s13n/AES42HAT/fw/model/I3C0.yaml

# Created from LPC865.svd

name: I3C0
description: I3C
groupName: I3C
registers:
  - name: MCONFIG
    description: Master Configuration Register
    addressOffset: 0
    size: 32
    access: read-write
    resetValue: 0
    resetMask: 4294967291
    fields:
      - name: MSTENA
        description: Master enable
        bitOffset: 0
        bitWidth: 2
        access: read-write
        enumeratedValues:
          - name: MASTER_OFF
            description: 'MASTER_OFF: Master is off (is not enabled). If MASTER_OFF
              is enabled, then the I3C module can only use slave mode.'
            value: 0
          - name: MASTER_ON
            description: 'MASTER_ON: Master is on (is enabled). When used from start-up,
              this I3C module is master by default (the main master). The module will
              control the bus unless the master is handed off. If the master is handed
              off, then MSTENA must move to 2 after that happens. The handoff means
              emitting GETACCMST and if accepted, the module will emit a STOP and
              set the MSTENA bit to 2 (or 0).'
            value: 1
          - name: MASTER_CAPABLE
            description: 'MASTER_CAPABLE: The I3C module is master-capable; however
              the module is operating as a slave now. When used from the start, the
              I3C module will start as a slave, but will be prepared to switch to
              master mode. To switch to master mode, the slave emits an Master Request
              (MR), or gets a GETACCMST CCC command and accepts it (to switch on the
              STOP).'
            value: 2
      - name: DISTO
        description: Disable Timeout
        bitOffset: 3
        bitWidth: 1
        access: read-write
      - name: HKEEP
        description: High-Keeper
        bitOffset: 4
        bitWidth: 2
        access: read-write
        enumeratedValues:
          - name: NONE
            description: 'NONE: Use PUR (Pull-Up Resistor). Hold SCL High.'
            value: 0
          - name: WIRED_IN
            description: 'WIRED_IN: Wired-in High Keeper controls; use pin_HK (High
              Keeper) controls.'
            value: 1
          - name: PASSIVE_SDA
            description: 'PASSIVE_SDA: Passive on SDA; can Hi-Z (high impedance) for
              Bus Free (IDLE) and hold.'
            value: 2
          - name: PASSIVE_ON_SDA_SCL
            description: 'PASSIVE_ON_SDA_SCL: Passive on SDA and SCL; can Hi-Z (high
              impedance) both for Bus Free (IDLE), and can Hi-Z SDA for hold.'
            value: 3
      - name: ODSTOP
        description: Open drain stop
        bitOffset: 6
        bitWidth: 1
        access: read-write
      - name: PPBAUD
        description: Push-pull baud rate
        bitOffset: 8
        bitWidth: 4
        access: read-write
      - name: PPLOW
        description: Push-Pull low
        bitOffset: 12
        bitWidth: 4
        access: read-write
      - name: ODBAUD
        description: Open drain baud rate
        bitOffset: 16
        bitWidth: 8
        access: read-write
      - name: ODHPP
        description: Open drain high push-pull
        bitOffset: 24
        bitWidth: 1
        access: read-write
      - name: SKEW
        description: Skew
        bitOffset: 25
        bitWidth: 3
        access: read-write
      - name: I2CBAUD
        description: I2C baud rate
        bitOffset: 28
        bitWidth: 4
        access: read-write
  - name: SCONFIG
    description: Slave Configuration Register
    addressOffset: 4
    size: 32
    access: read-write
    resetValue: 0
    resetMask: 4278125439
    fields:
      - name: SLVENA
        description: Slave enable
        bitOffset: 0
        bitWidth: 1
        access: read-write
      - name: NACK
        description: Not acknowledge
        bitOffset: 1
        bitWidth: 1
        access: read-write
      - name: MATCHSS
        description: Match START or STOP
        bitOffset: 2
        bitWidth: 1
        access: read-write
      - name: S0IGNORE
        description: S0/S1 errors ignore
        bitOffset: 3
        bitWidth: 1
        access: read-write
      - name: DDROK
        description: Double Data Rate OK
        bitOffset: 4
        bitWidth: 1
        access: read-write
      - name: IDRAND
        description: ID random
        bitOffset: 8
        bitWidth: 1
        access: read-write
      - name: OFFLINE
        description: Offline
        bitOffset: 9
        bitWidth: 1
        access: read-write
      - name: BAMATCH
        description: Bus available match
        bitOffset: 16
        bitWidth: 8
        access: read-write
      - name: SADDR
        description: Static address
        bitOffset: 25
        bitWidth: 7
        access: read-write
  - name: SSTATUS
    description: Slave Status Register
    addressOffset: 8
    size: 32
    access: read-write
    resetValue: 4096
    resetMask: 4224188287
    fields:
      - name: STNOTSTOP
        description: Status not stop
        bitOffset: 0
        bitWidth: 1
        access: read-only
      - name: STMSG
        description: Status message
        bitOffset: 1
        bitWidth: 1
        access: read-only
      - name: STCCCH
        description: Status Common Command Code Handler
        bitOffset: 2
        bitWidth: 1
        access: read-only
      - name: STREQRD
        description: Status required
        bitOffset: 3
        bitWidth: 1
        access: read-only
      - name: STREQWR
        description: Status request write
        bitOffset: 4
        bitWidth: 1
        access: read-only
      - name: STDAA
        description: Status Dynamic Address Assignment
        bitOffset: 5
        bitWidth: 1
        access: read-only
      - name: STHDR
        description: Status High Data Rate
        bitOffset: 6
        bitWidth: 1
        access: read-only
      - name: START
        description: Start
        bitOffset: 8
        bitWidth: 1
        access: read-write
      - name: MATCHED
        description: Matched
        bitOffset: 9
        bitWidth: 1
        access: read-write
      - name: STOP
        description: Stop
        bitOffset: 10
        bitWidth: 1
        access: read-write
      - name: RX_PEND
        description: Received message pending
        bitOffset: 11
        bitWidth: 1
        access: read-only
      - name: TXNOTFULL
        description: Transmit buffer is not full
        bitOffset: 12
        bitWidth: 1
        access: read-only
      - name: DACHG
        description: DACHG
        bitOffset: 13
        bitWidth: 1
        access: read-write
      - name: CCC
        description: Common Command Code
        bitOffset: 14
        bitWidth: 1
        access: read-write
      - name: ERRWARN
        description: Error warning
        bitOffset: 15
        bitWidth: 1
        access: read-only
      - name: HDRMATCH
        description: High Data Rate command match
        bitOffset: 16
        bitWidth: 1
        access: read-write
      - name: CHANDLED
        description: Common-Command-Code handled
        bitOffset: 17
        bitWidth: 1
        access: read-write
      - name: EVENT
        description: Event
        bitOffset: 18
        bitWidth: 1
        access: read-write
      - name: EVDET
        description: Event details
        bitOffset: 20
        bitWidth: 2
        access: read-only
        enumeratedValues:
          - name: NONE
            description: 'NONE: no event or no pending event'
            value: 0
          - name: NO_REQUEST
            description: 'NO_REQUEST: Request not sent yet. Either there was no START
              yet, or is waiting for Bus-Available or Bus-Idle (HJ).'
            value: 1
          - name: NACKED
            description: 'NACKED: Not acknowledged(Request sent and NACKed); the module
              will try again.'
            value: 2
          - name: ACKED
            description: 'ACKED: Acknowledged (Request sent and ACKed), so Done (unless
              the time control data is still being sent).'
            value: 3
      - name: IBIDIS
        description: In-Band Interrupts are disabled
        bitOffset: 24
        bitWidth: 1
        access: read-only
      - name: MRDIS
        description: Master requests are disabled
        bitOffset: 25
        bitWidth: 1
        access: read-only
      - name: HJDIS
        description: Hot-Join is disabled
        bitOffset: 27
        bitWidth: 1
        access: read-only
      - name: ACTSTATE
        description: Activity state from Common Command Codes (CCC)
        bitOffset: 28
        bitWidth: 2
        access: read-only
        enumeratedValues:
          - name: NO_LATENCY
            description: 'NO_LATENCY: normal bus operations'
            value: 0
          - name: LATENCY_1MS
            description: 'LATENCY_1MS: 1 ms of latency'
            value: 1
          - name: LATENCY_100MS
            description: 'LATENCY_100MS: 100 ms of latency'
            value: 2
          - name: LATENCY_10S
            description: 'LATENCY_10S: 10 seconds of latency'
            value: 3
      - name: TIMECTRL
        description: Time control
        bitOffset: 30
        bitWidth: 2
        access: read-only
        enumeratedValues:
          - name: NO_TIME_CONTROL
            description: 'NO_TIME_CONTROL: No time control is enabled'
            value: 0
          - name: ASYNC_MODE
            description: 'ASYNC_MODE: Asynchronous standard mode (0) is enabled'
            value: 2
  - name: SCTRL
    description: Slave Control Register
    addressOffset: 12
    size: 32
    access: read-write
    resetValue: 0
    resetMask: 4282384131
    fields:
      - name: EVENT
        description: EVENT
        bitOffset: 0
        bitWidth: 2
        access: read-write
        enumeratedValues:
          - name: NORMAL_MODE
            description: 'NORMAL_MODE: If EVENT is set to 0 after was a non-0 value,
              event processing will cancel if the event processing has not yet started;
              if event processing has already been started, then event processing
              will not be be cancelled.'
            value: 0
          - name: IBI
            description: 'IBI: Start an In-Band Interrupt. This will try to push an
              IBI interrupt onto the I3C bus. If data is associated with the IBI,
              then the data will be read from the SCTRL.IBIDATA field. If time control
              is enabled, then this data will also include any time control-related
              bytes; additionally, the IBIDATA byte will have bit 7 set to 1 automatically
              (as is required for time control). The IBI interrupt will occur after
              the 1st (mandatory) IBIDATA, if any.'
            value: 1
          - name: MASTER_REQUEST
            description: 'MASTER_REQUEST: Start a Master-Request.'
            value: 2
          - name: HOT_JOIN_REQUEST
            description: 'HOT_JOIN_REQUEST: Start a Hot-Join request. A Hot-Join Request
              should only be used when the device is powered on after the I3C bus
              is already powered up, or when the device is connected using hot insertion
              methods (the device is powered up when it is physically inserted onto
              the powered-up I3C bus). The hot join will wait for Bus Idle, and SCTRL.EVENT=HOT_JOIN_REQUEST
              must be set before the slave enable (SCONFIG.SLVENA).'
            value: 3
      - name: IBIDATA
        description: In-Band Interrupt data
        bitOffset: 8
        bitWidth: 8
        access: read-write
      - name: PENDINT
        description: Pending interrupt
        bitOffset: 16
        bitWidth: 4
        access: read-write
      - name: ACTSTATE
        description: Activity state (of slave)
        bitOffset: 20
        bitWidth: 2
        access: read-write
      - name: VENDINFO
        description: Vendor information
        bitOffset: 24
        bitWidth: 8
        access: read-write
  - name: SINTSET
    description: Slave Interrupt Set Register
    addressOffset: 16
    size: 32
    access: read-write
    resetValue: 0
    resetMask: 524032
    fields:
      - name: START
        description: Start interrupt enable
        bitOffset: 8
        bitWidth: 1
        access: read-write
      - name: MATCHED
        description: Match interrupt enable
        bitOffset: 9
        bitWidth: 1
        access: read-write
      - name: STOP
        description: Stop interrupt enable
        bitOffset: 10
        bitWidth: 1
        access: read-write
      - name: RXPEND
        description: Receive interrupt enable
        bitOffset: 11
        bitWidth: 1
        access: read-write
      - name: TXSEND
        description: Transmit interrupt enable
        bitOffset: 12
        bitWidth: 1
        access: read-write
      - name: DACHG
        description: Dynamic address change interrupt enable
        bitOffset: 13
        bitWidth: 1
        access: read-write
      - name: CCC
        description: Common Command Code (CCC) (that was not handled by I3C module)
          interrupt enable
        bitOffset: 14
        bitWidth: 1
        access: read-write
      - name: ERRWARN
        description: Error/warning interrupt enable
        bitOffset: 15
        bitWidth: 1
        access: read-write
      - name: DDRMATCHED
        description: Double Data Rate (DDR) interrupt enable
        bitOffset: 16
        bitWidth: 1
        access: read-write
      - name: CHANDLED
        description: Common Command Code (CCC) (that was handled by I3C module) interrupt
          enable
        bitOffset: 17
        bitWidth: 1
        access: read-write
      - name: EVENT
        description: Event interrupt enable
        bitOffset: 18
        bitWidth: 1
        access: read-write
  - name: SINTCLR
    description: Slave Interrupt Clear Register
    addressOffset: 20
    size: 32
    access: read-write
    resetValue: 0
    resetMask: 0
    modifiedWriteValues: oneToClear
    fields:
      - name: START
        description: START interrupt enable clear
        bitOffset: 8
        bitWidth: 1
        access: read-write
        modifiedWriteValues: oneToClear
      - name: MATCHED
        description: MATCHED interrupt enable clear
        bitOffset: 9
        bitWidth: 1
        access: read-write
        modifiedWriteValues: oneToClear
      - name: STOP
        description: STOP interrupt enable clear
        bitOffset: 10
        bitWidth: 1
        access: read-write
        modifiedWriteValues: oneToClear
      - name: RXPEND
        description: RXPEND interrupt enable clear
        bitOffset: 11
        bitWidth: 1
        access: read-write
        modifiedWriteValues: oneToClear
      - name: TXSEND
        description: TXSEND interrupt enable clear
        bitOffset: 12
        bitWidth: 1
        access: read-write
        modifiedWriteValues: oneToClear
      - name: DACHG
        description: DACHG interrupt enable clear
        bitOffset: 13
        bitWidth: 1
        access: read-write
        modifiedWriteValues: oneToClear
      - name: CCC
        description: CCC interrupt enable clear
        bitOffset: 14
        bitWidth: 1
        access: read-write
        modifiedWriteValues: oneToClear
      - name: ERRWARN
        description: ERRWARN interrupt enable clear
        bitOffset: 15
        bitWidth: 1
        access: read-write
        modifiedWriteValues: oneToClear
      - name: DDRMATCHED
        description: DDRMATCHED interrupt enable clear
        bitOffset: 16
        bitWidth: 1
        access: read-write
        modifiedWriteValues: oneToClear
      - name: CHANDLED
        description: CHANDLED interrupt enable clear
        bitOffset: 17
        bitWidth: 1
        access: read-write
        modifiedWriteValues: oneToClear
      - name: EVENT
        description: EVENT interrupt enable clear
        bitOffset: 18
        bitWidth: 1
        access: read-write
        modifiedWriteValues: oneToClear
  - name: SINTMASKED
    description: Slave Interrupt Mask Register
    addressOffset: 24
    size: 32
    access: read-only
    resetValue: 4096
    resetMask: 524032
    fields:
      - name: START
        description: START interrupt mask
        bitOffset: 8
        bitWidth: 1
        access: read-only
      - name: MATCHED
        description: MATCHED interrupt mask
        bitOffset: 9
        bitWidth: 1
        access: read-only
      - name: STOP
        description: STOP interrupt mask
        bitOffset: 10
        bitWidth: 1
        access: read-only
      - name: RXPEND
        description: RXPEND interrupt mask
        bitOffset: 11
        bitWidth: 1
        access: read-only
      - name: TXSEND
        description: TXSEND interrupt mask
        bitOffset: 12
        bitWidth: 1
        access: read-only
      - name: DACHG
        description: DACHG interrupt mask
        bitOffset: 13
        bitWidth: 1
        access: read-only
      - name: CCC
        description: CCC interrupt mask
        bitOffset: 14
        bitWidth: 1
        access: read-only
      - name: ERRWARN
        description: ERRWARN interrupt mask
        bitOffset: 15
        bitWidth: 1
        access: read-only
      - name: DDRMATCHED
        description: DDRMATCHED interrupt mask
        bitOffset: 16
        bitWidth: 1
        access: read-only
      - name: CHANDLED
        description: CHANDLED interrupt mask
        bitOffset: 17
        bitWidth: 1
        access: read-only
      - name: EVENT
        description: EVENT interrupt mask
        bitOffset: 18
        bitWidth: 1
        access: read-only
  - name: SERRWARN
    description: Slave Errors and Warnings Register
    addressOffset: 28
    size: 32
    access: read-write
    resetValue: 0
    resetMask: 200479
    fields:
      - name: ORUN
        description: Overrun error
        bitOffset: 0
        bitWidth: 1
        access: read-write
      - name: URUN
        description: Underrun error
        bitOffset: 1
        bitWidth: 1
        access: read-write
      - name: URUNNACK
        description: Underrun and Not Acknowledged (NACKed) error
        bitOffset: 2
        bitWidth: 1
        access: read-write
      - name: TERM
        description: Terminated error
        bitOffset: 3
        bitWidth: 1
        access: read-write
      - name: INVSTART
        description: Invalid start error
        bitOffset: 4
        bitWidth: 1
        access: read-write
      - name: SPAR
        description: SDR parity error
        bitOffset: 8
        bitWidth: 1
        access: read-write
      - name: HPAR
        description: HDR parity error
        bitOffset: 9
        bitWidth: 1
        access: read-write
      - name: HCRC
        description: HDR-DDR CRC error
        bitOffset: 10
        bitWidth: 1
        access: read-write
      - name: S0S1
        description: S0 or S1 error
        bitOffset: 11
        bitWidth: 1
        access: read-write
      - name: OREAD
        description: Over-read error
        bitOffset: 16
        bitWidth: 1
        access: read-write
      - name: OWRITE
        description: Over-write error
        bitOffset: 17
        bitWidth: 1
        access: read-write
  - name: SDMACTRL
    description: Slave DMA Control Register
    addressOffset: 32
    size: 32
    access: read-write
    resetValue: 16
    resetMask: 63
    fields:
      - name: DMAFB
        description: DMA Read (From-bus) trigger
        bitOffset: 0
        bitWidth: 2
        access: read-write
        enumeratedValues:
          - name: NOT_USED
            description: DMA not used
            value: 0
          - name: ENABLE_ONE_FRAME
            description: DMA is enabled for 1 frame
            value: 1
          - name: ENABLE
            description: DMA enable
            value: 2
      - name: DMATB
        description: DMA Write (To-bus) trigger
        bitOffset: 2
        bitWidth: 2
        access: read-write
        enumeratedValues:
          - name: NOT_USED
            description: 'NOT_USED: DMA is not used'
            value: 0
          - name: ENABLE_ONE_FRAME
            description: 'ENABLE_ONE_FRAME: DMA is enabled for 1 Frame (ended by DMA
              or terminated). DMATB auto-clears on a STOP or START (see the Match
              START or STOP bit (SCONFIG.MATCHSS).'
            value: 1
          - name: ENABLE
            description: 'ENABLE: DMA is enabled until turned off. Normally, ENABLE
              should only be used with Master Message mode.'
            value: 2
      - name: DMAWIDTH
        description: Width of DMA operations
        bitOffset: 4
        bitWidth: 2
        access: read-write
        enumeratedValues:
          - name: BYTE
            description: BYTE
            value: 0
          - name: BYTE_AGAIN
            description: BYTE_AGAIN
            value: 1
          - name: HALF_WORD
            description: 'HALF_WORD: Half word (16 bits). This will make sure that
              2 bytes are free/available in the FIFO.'
            value: 2
  - name: SDATACTRL
    description: Slave Data Control Register
    addressOffset: 44
    size: 32
    access: read-write
    resetValue: 2147483696
    resetMask: 3743351031
    fields:
      - name: FLUSHTB
        description: Flush the to-bus buffer/FIFO
        bitOffset: 0
        bitWidth: 1
        access: write-only
      - name: FLUSHFB
        description: Flushes the from-bus buffer/FIFO
        bitOffset: 1
        bitWidth: 1
        access: write-only
      - name: UNLOCK
        description: Unlock
        bitOffset: 3
        bitWidth: 1
        access: write-only
      - name: TXTRIG
        description: Trigger level for TX FIFO emptiness
        bitOffset: 4
        bitWidth: 2
        access: read-write
        enumeratedValues:
          - name: TRIGGREMPTY
            description: Trigger on empty
            value: 0
          - name: TRIGGRONEFOURTH
            description: Trigger on full or less
            value: 1
          - name: TRIGGRONEHALF
            description: Trigger on .5 full or less
            value: 2
          - name: TRIGGRONELESS
            description: Trigger on 1 less than full or less (Default)
            value: 3
      - name: RXTRIG
        description: Trigger level for RX FIFO fullness
        bitOffset: 6
        bitWidth: 2
        access: read-write
        enumeratedValues:
          - name: TRIGGRNOTEMPTY
            description: Trigger on not empty
            value: 0
          - name: TRIGGRONEFOURTH
            description: Trigger on or more full
            value: 1
          - name: TRIGGRONEHALF
            description: Trigger on .5 or more full
            value: 2
          - name: TRIGGRTHREEFOURTHS
            description: Trigger on 3/4 or more full
            value: 3
      - name: TXCOUNT
        description: Count of bytes in TX
        bitOffset: 16
        bitWidth: 5
        access: read-only
      - name: RXCOUNT
        description: Count of bytes in RX
        bitOffset: 24
        bitWidth: 5
        access: read-only
      - name: TXFULL
        description: TX is full
        bitOffset: 30
        bitWidth: 1
        access: read-only
        enumeratedValues:
          - name: TXISNOTFULL
            description: TX is not full
            value: 0
          - name: TXISFULL
            description: TX is full
            value: 1
      - name: RXEMPTY
        description: RX is empty
        bitOffset: 31
        bitWidth: 1
        access: read-only
        enumeratedValues:
          - name: RXISNOTEMPTY
            description: RX is not empty
            value: 0
          - name: RXISEMPTY
            description: RX is empty
            value: 1
  - name: SWDATAB
    description: Slave Write Data Byte Register
    addressOffset: 48
    size: 32
    access: write-only
    resetValue: 0
    resetMask: 0
    fields:
      - name: DATA
        description: The data byte to send to the master
        bitOffset: 0
        bitWidth: 8
        access: write-only
      - name: END
        description: End
        bitOffset: 8
        bitWidth: 1
        access: write-only
      - name: END_ALSO
        description: End also
        bitOffset: 16
        bitWidth: 1
        access: write-only
  - name: SWDATABE
    description: Slave Write Data Byte End
    addressOffset: 52
    size: 32
    access: write-only
    resetValue: 0
    resetMask: 0
    fields:
      - name: DATA
        description: The data byte to send to the master
        bitOffset: 0
        bitWidth: 8
        access: write-only
  - name: SWDATAH
    description: Slave Write Data Half-word Register
    addressOffset: 56
    size: 32
    access: write-only
    resetValue: 0
    resetMask: 0
    fields:
      - name: DATA0
        description: The 1st byte to send to the master
        bitOffset: 0
        bitWidth: 8
        access: write-only
      - name: DATA1
        description: The 2nd byte to send to the master
        bitOffset: 8
        bitWidth: 8
        access: write-only
      - name: END
        description: End of message
        bitOffset: 16
        bitWidth: 1
        access: write-only
  - name: SWDATAHE
    description: Slave Write Data Half-word End Register
    addressOffset: 60
    size: 32
    access: write-only
    resetValue: 0
    resetMask: 0
    fields:
      - name: DATA0
        description: The 1st byte to send to the master
        bitOffset: 0
        bitWidth: 8
        access: write-only
      - name: DATA1
        description: The 2nd byte to send to the master
        bitOffset: 8
        bitWidth: 8
        access: write-only
  - name: SRDATAB
    description: Slave Read Data Byte Register
    addressOffset: 64
    size: 32
    access: read-only
    resetValue: 0
    resetMask: 255
    fields:
      - name: DATA0
        description: Byte read from the master
        bitOffset: 0
        bitWidth: 8
        access: read-only
  - name: SRDATAH
    description: Slave Read Data Half-word Register
    addressOffset: 72
    size: 32
    access: read-only
    resetValue: 0
    resetMask: 65535
    fields:
      - name: LSB
        description: The 1st byte read from the slave
        bitOffset: 0
        bitWidth: 8
        access: read-only
      - name: MSB
        description: The 2nd byte read from the slave
        bitOffset: 8
        bitWidth: 8
        access: read-only
  - name: SWDATAB1
    description: Target Write Data Byte Register
    addressOffset: 84
    size: 32
    access: write-only
    resetValue: 0
    resetMask: 65535
    fields:
      - name: DATA
        description: The data byte rto send to controller
        bitOffset: 0
        bitWidth: 8
        access: write-only
  - name: SCAPABILITIES
    description: Slave Capabilities Register
    addressOffset: 96
    size: 32
    access: read-only
    resetValue: 3896508024
    resetMask: 4294967295
    fields:
      - name: IDENA
        description: ID 48b handler
        bitOffset: 0
        bitWidth: 2
        access: read-only
        enumeratedValues:
          - name: APPLICATION
            description: 'APPLICATION: Application handles ID 48b'
            value: 0
          - name: HW
            description: 'HW: Hardware handles ID 48b'
            value: 1
          - name: HW_BUT
            description: 'HW_BUT: in hardware but the I3C module instance handles
              ID 48b.'
            value: 2
          - name: PARTNO
            description: 'PARTNO: a part number register (PARTNO) handles ID 48b'
            value: 3
      - name: IDREG
        description: ID register
        bitOffset: 2
        bitWidth: 4
        access: read-only
      - name: HDRSUPP
        description: HDR support
        bitOffset: 6
        bitWidth: 3
        access: read-only
      - name: MASTER
        description: Master
        bitOffset: 9
        bitWidth: 1
        access: read-only
        enumeratedValues:
          - name: MASTERNOTSUPPORTED
            description: 'MASTERNOTSUPPORTED: master capability is not supported.'
            value: 0
          - name: MASTERSUPPORTED
            description: 'MASTERSUPPORTED: master capability is supported.'
            value: 1
      - name: SADDR
        description: Static address
        bitOffset: 10
        bitWidth: 2
        access: read-only
        enumeratedValues:
          - name: NO_STATIC
            description: 'NO_STATIC: No static address'
            value: 0
          - name: STATIC
            description: 'STATIC: Static address is fixed in hardware'
            value: 1
          - name: HW_CONTROL
            description: 'HW_CONTROL: Hardware controls the static address dynamically
              (for example, from the pin strap)'
            value: 2
          - name: CONFIG
            description: 'CONFIG: SCONFIG register supplies the static address'
            value: 3
      - name: CCCHANDLE
        description: Common Command Codes (CCC) handling
        bitOffset: 12
        bitWidth: 4
        access: read-only
      - name: IBI_MR_HJ
        description: In-Band Interrupts, Master Requests, Hot Join events
        bitOffset: 16
        bitWidth: 5
        access: read-only
      - name: TIMECTRL
        description: Time control
        bitOffset: 21
        bitWidth: 1
        access: read-only
        enumeratedValues:
          - name: NO_TIME_CONTROL_TYPE
            description: 'NO_TIME_CONTROL_TYPE: No time control is enabled'
            value: 0
          - name: ATLEAST1_TIME_CONTROL
            description: 'ATLEAST1_TIME_CONTROL: at least one time-control type is
              supported'
            value: 1
      - name: EXTFIFO
        description: External FIFO
        bitOffset: 23
        bitWidth: 3
        access: read-only
        enumeratedValues:
          - name: STD_EXT_FIFO
            description: 'STD_EXT_FIFO: standard available/free external FIFO'
            value: 1
      - name: FIFOTX
        description: FIFO transmit
        bitOffset: 26
        bitWidth: 2
        access: read-only
        enumeratedValues:
          - name: FIFO_2BYTE
            description: 'FIFO_2BYTE: 2-byte TX FIFO, the default FIFO transmit value
              (FIFOTX)'
            value: 0
          - name: FIFO_4BYTE
            description: 'FIFO_4BYTE: 4-byte TX FIFO'
            value: 1
          - name: FIFO_8BYTE
            description: 'FIFO_8BYTE: 8-byte TX FIFO'
            value: 2
          - name: FIFO_16BYTE
            description: 'FIFO_16BYTE: 16-byte TX FIFO'
            value: 3
      - name: FIFORX
        description: FIFO receive
        bitOffset: 28
        bitWidth: 2
        access: read-only
        enumeratedValues:
          - name: FIFO_2BYTE
            description: 'FIFO_2BYTE: 2 (or 3)-byte RX FIFO, the default FIFO receive
              value (FIFORX)'
            value: 0
          - name: FIFO_4BYTE
            description: 'FIFO_4BYTE: 4-byte RX FIFO'
            value: 1
          - name: FIFO_8BYTE
            description: 'FIFO_8BYTE: 8-byte RX FIFO'
            value: 2
          - name: FIFO_16BYTE
            description: 'FIFO_16BYTE: 16-byte RX FIFO'
            value: 3
      - name: INT
        description: INT
        bitOffset: 30
        bitWidth: 1
        access: read-only
        enumeratedValues:
          - name: INTERRUPTSNO
            description: Interrupts are not supported
            value: 0
          - name: INTERRUPTSYES
            description: Interrupts are supported
            value: 1
      - name: DMA
        description: DMA
        bitOffset: 31
        bitWidth: 1
        access: read-only
        enumeratedValues:
          - name: DMANO
            description: DMA is not supported
            value: 0
          - name: DMAYES
            description: DMA is supported
            value: 1
  - name: SDYNADDR
    description: Slave Dynamic Address Register
    addressOffset: 100
    size: 32
    access: read-write
    resetValue: 0
    resetMask: 4294902015
    fields:
      - name: DAVALID
        description: DAVALID
        bitOffset: 0
        bitWidth: 1
        access: read-write
        enumeratedValues:
          - name: DANOTASSIGNED
            description: 'DANOTASSIGNED: a Dynamic Address is not assigned'
            value: 0
          - name: DAASSIGNED
            description: 'DAASSIGNED: a Dynamic Address is assigned'
            value: 1
      - name: DADDR
        description: Dynamic address
        bitOffset: 1
        bitWidth: 7
        access: read-write
      - name: MAPIDX
        description: Mapped Dynamic Address
        bitOffset: 8
        bitWidth: 4
        access: write-only
      - name: MAPSA
        description: Map a Static Address
        bitOffset: 12
        bitWidth: 1
        access: write-only
      - name: KEY
        description: Key
        bitOffset: 16
        bitWidth: 16
        access: read-write
  - name: SMAXLIMITS
    description: Slave Maximum Limits Register
    addressOffset: 104
    size: 32
    access: read-write
    resetValue: 0
    resetMask: 4293984240
    fields:
      - name: MAXRD
        description: Maximum read length
        bitOffset: 0
        bitWidth: 12
        access: read-write
      - name: MAXWR
        description: Maximum write length
        bitOffset: 16
        bitWidth: 12
        access: read-write
  - name: SIDPARTNO
    description: Slave ID Part Number Register
    addressOffset: 108
    size: 32
    access: read-write
    resetValue: 0
    resetMask: 4294967295
    fields:
      - name: PARTNO
        description: Part number
        bitOffset: 0
        bitWidth: 32
        access: read-write
  - name: SIDEXT
    description: Slave ID Extension Register
    addressOffset: 112
    size: 32
    access: read-write
    resetValue: 0
    resetMask: 16776975
    fields:
      - name: DCR
        description: Device Characteristic Register
        bitOffset: 8
        bitWidth: 8
        access: read-write
      - name: BCR
        description: Bus Characteristics Register
        bitOffset: 16
        bitWidth: 8
        access: read-write
  - name: SVENDORID
    description: Slave Vendor ID Register
    addressOffset: 116
    size: 32
    access: read-write
    resetValue: 283
    resetMask: 32767
    fields:
      - name: VID
        description: Vendor ID
        bitOffset: 0
        bitWidth: 15
        access: read-write
  - name: STCCLOCK
    description: Slave Time Control Clock Register
    addressOffset: 120
    size: 32
    access: read-write
    resetValue: 532
    resetMask: 65535
    fields:
      - name: ACCURACY
        description: Clock accuracy
        bitOffset: 0
        bitWidth: 8
        access: read-write
      - name: FREQ
        description: Clock frequency
        bitOffset: 8
        bitWidth: 8
        access: read-write
  - name: SMSGMAPADDR
    description: Slave Message-Mapped Address Register
    addressOffset: 124
    size: 32
    access: read-only
    resetValue: 532
    resetMask: 65535
    fields:
      - name: MAPLAST
        description: Matched address index
        bitOffset: 0
        bitWidth: 4
        access: read-only
      - name: MAPLASTM1
        description: Previous match index 1
        bitOffset: 8
        bitWidth: 4
        access: read-only
      - name: MAPLASTM2
        description: Previous match index 2
        bitOffset: 16
        bitWidth: 4
        access: read-only
  - name: MCTRL
    description: Master Main Control Register
    addressOffset: 132
    size: 32
    access: read-write
    resetValue: 0
    resetMask: 16777207
    fields:
      - name: REQUEST
        description: Request
        bitOffset: 0
        bitWidth: 3
        access: read-write
        enumeratedValues:
          - name: NONE
            description: "NONE: Returns to this when finished with any request. The
              MSTATUS register indicates the master's state. See also AutoIBI mode.
              NONE is only written as 0: when setting RDTERM to 1 (to stop a read
              in progress) or when setting IBI reponse field (IBIRESP) for MSG use"
            value: 0
          - name: EMITSTARTADDR
            description: 'EMITSTARTADDR: Emit START with address and direction from
              a stopped state or in the middle of a Single Data Rate (SDR) message.
              If from a stopped state (IDLE), then emit start may be prevented by
              an event (like IBI, MR, HJ), in which case the appropriate interrupt
              is signaled; note that Emit START can be resubmitted.'
            value: 1
          - name: EMITSTOP
            description: 'EMITSTOP: Emit a STOP on bus. Must be in Single Data Rate
              (SDR) mode. If in Dynamic Address Assignment (DAA) mode, Emit stop will
              exit DAA mode.'
            value: 2
          - name: IBIACKNACK
            description: 'IBIACKNACK: Manual In-Band Interrupt (IBI) Acknowledge (ACK)
              or Not Acknowledge (NACK). When IBIRESP has indicated a hold on an In-Band
              Interrupt to allow a manual decision, this request completes it. Uses
              IBIRESP to provide the information.'
            value: 3
          - name: PROCESSDAA
            description: 'PROCESSDAA: If not in Dynamic Address Assignment (DAA) mode
              now, will issue START, 7E, ENTDAA, and then will emit 7E/R to process
              each slave. Will stop just before the new Dynamic Address (DA) is to
              be emitted. The next Process DAA request will use the Addr field as
              the new DA to assign. If NACKed on the 7E/R, then the interrupt will
              indicate this situation, and a STOP will be emitted.'
            value: 4
          - name: FORCEEXIT
            description: 'FORCEEXIT and IBHR: Emit an Exit Pattern from any state,
              but end Double Data Rate (DDR) (including MSGDDR), if in DDR mode now.
              Includes a STOP afterward. If TYPE != 0, then it will perform an IBHR
              (In-Band Hardware Reset). If TYPE=2, then it does a normal reset (DEFRST
              can prevent the reset). If TYPE=3, it does a forced reset (will always
              reset).'
            value: 6
          - name: AUTOIBI
            description: 'AUTOIBI: Hold in a stopped state, but auto-emit START,7E
              when the slave is holding down SDA to get an In-Band Interrupt (IBI).
              Actual In-Band Interrupt handling is defined by IBIRESP.'
            value: 7
      - name: TYPE
        description: Bus type with START
        bitOffset: 4
        bitWidth: 2
        access: read-write
        enumeratedValues:
          - name: I3C
            description: 'I3C: Normally the SDR mode of I3C. For ForceExit, the Exit
              pattern.'
            value: 0
          - name: I2C
            description: 'I2C: Normally the Standard I2C protocol.'
            value: 1
          - name: DDR
            description: 'DDR: (Double Data Rate): Normally the HDR-DDR mode of I3C.
              Enter DDR mode (7E and then ENTHDR0), if the module is not already in
              DDR mode. The 1st byte written to the TX FIFO should be a command, and
              should already be in the FIFO. To end DDR mode, use ForceExit. For ForceExit,
              the normal IBHR (In-Band Hardware Reset).'
            value: 2
          - name: FORCEDIBHR
            description: For ForcedExit, this is forced IBHR.
            value: 3
      - name: IBIRESP
        description: In-Band Interrupt (IBI) response
        bitOffset: 6
        bitWidth: 2
        access: read-write
        enumeratedValues:
          - name: ACK
            description: 'ACK: Acknowledge. A mandatory byte (or not) is decided by
              the Master In-band Interrupt Registry and Rules Register (MIBIRULES).
              To limit the maximum number of IBI bytes, configure the Read Termination
              field (MCTRL.RDTERM).'
            value: 0
          - name: NACK
            description: 'NACK: Not acknowledge'
            value: 1
          - name: ACK_WITH_MANDATORY
            description: 'ACK_WITH_MANDATORY: Acknowledge with mandatory byte (ignores
              the MIBIRULES register). Acknowledge with mandatory byte should not
              be used, unless only slaves with a mandatory byte can cause an In-Band
              Interrupt.'
            value: 2
          - name: MANUAL
            description: 'MANUAL: stop and wait for a decision using the IBIAckNack
              request'
            value: 3
      - name: DIR
        description: DIR
        bitOffset: 8
        bitWidth: 1
        access: read-write
        enumeratedValues:
          - name: DIRWRITE
            description: 'DIRWRITE: Write'
            value: 0
          - name: DIRREAD
            description: 'DIRREAD: Read'
            value: 1
      - name: ADDR
        description: ADDR
        bitOffset: 9
        bitWidth: 7
        access: read-write
      - name: RDTERM
        description: Read terminate
        bitOffset: 16
        bitWidth: 8
        access: read-write
  - name: MSTATUS
    description: Master Status Register
    addressOffset: 136
    size: 32
    access: read-write
    resetValue: 4096
    resetMask: 4278763511
    fields:
      - name: STATE
        description: State of the master
        bitOffset: 0
        bitWidth: 3
        access: read-only
        enumeratedValues:
          - name: IDLE
            description: 'IDLE: the bus has STOPped.'
            value: 0
          - name: SLVREQ
            description: 'SLVREQ: (Slave Request state) the bus has STOPped but a
              slave is holding SDA low. If using auto-emit IBI (MCTRL.AutoIBI), then
              the master will not stay in the Slave Request state.'
            value: 1
          - name: MSGSDR
            description: 'MSGSDR: in Single Data Rate (SDR) Message state (from using
              MWMSG_SDR)'
            value: 2
          - name: NORMACT
            description: 'NORMACT: normal active Single Data Rate (SDR) state (from
              using MCTRL and MWDATAn and MRDATAn registers). The master will stay
              in the NORMACT state until a STOP is issued.'
            value: 3
          - name: DDR
            description: 'MSGDDR: in Double Data Rate (DDR) Message mode (from using
              MWMSG_DDR or using the normal method with DDR). The master will stay
              in the DDR state, until the master exits using EXIT (emits the Exit
              pattern).'
            value: 4
          - name: DAA
            description: 'DAA: in Enter Dynamic Address Assignment (ENTDAA) mode'
            value: 5
          - name: IBIACK
            description: 'IBIACK: waiting for an In-Band Interrupt (IBI) ACK/NACK
              decision'
            value: 6
          - name: IBIRCV
            description: 'IBIRCV: Receiving an In-Band Interrupt (IBI); this IBIRCV
              state is used after IBI/MR/HJ has won the arbitration, and IBIRCV state
              is also used for IBI mandatory byte (if any) and any bytes that follow.'
            value: 7
      - name: BETWEEN
        description: Between messages or Dynamic Address Assignments (DAA)
        bitOffset: 4
        bitWidth: 1
        access: read-only
      - name: NACKED
        description: Not acknowledged
        bitOffset: 5
        bitWidth: 1
        access: read-only
      - name: IBITYPE
        description: In-Band Interrupt (IBI) type
        bitOffset: 6
        bitWidth: 2
        access: read-only
        enumeratedValues:
          - name: NONE
            description: 'NONE: cleared when IBI Won bit (MSTATUS.IBIWON) is cleared'
            value: 0
          - name: IBI
            description: 'IBI: In-Band Interrupt'
            value: 1
          - name: MR
            description: 'MR: Master Request'
            value: 2
          - name: HJ
            description: 'HJ: Hot-Join'
            value: 3
      - name: SLVSTART
        description: Slave start
        bitOffset: 8
        bitWidth: 1
        access: read-write
      - name: MCTRLDONE
        description: Master control done
        bitOffset: 9
        bitWidth: 1
        access: read-write
      - name: COMPLETE
        description: COMPLETE
        bitOffset: 10
        bitWidth: 1
        access: read-write
      - name: RXPEND
        description: RXPEND
        bitOffset: 11
        bitWidth: 1
        access: read-only
      - name: TXNOTFULL
        description: TX buffer/FIFO not yet full
        bitOffset: 12
        bitWidth: 1
        access: read-only
      - name: IBIWON
        description: In-Band Interrupt (IBI) won
        bitOffset: 13
        bitWidth: 1
        access: read-write
      - name: ERRWARN
        description: Error or warning
        bitOffset: 15
        bitWidth: 1
        access: read-only
      - name: NOWMASTER
        description: Now master (now this module is a master)
        bitOffset: 19
        bitWidth: 1
        access: read-write
      - name: IBIADDR
        description: IBI address
        bitOffset: 24
        bitWidth: 7
        access: read-only
  - name: MIBIRULES
    description: Master In-band Interrupt Registry and Rules Register
    addressOffset: 140
    size: 32
    access: read-write
    resetValue: 0
    resetMask: 4294967295
    fields:
      - name: ADDR0
        description: ADDR0
        bitOffset: 0
        bitWidth: 6
        access: read-write
      - name: ADDR1
        description: ADDR1
        bitOffset: 6
        bitWidth: 6
        access: read-write
      - name: ADDR2
        description: ADDR2
        bitOffset: 12
        bitWidth: 6
        access: read-write
      - name: ADDR3
        description: ADDR3
        bitOffset: 18
        bitWidth: 6
        access: read-write
      - name: ADDR4
        description: ADDR4
        bitOffset: 24
        bitWidth: 6
        access: read-write
      - name: MSB0
        description: Set Most Significant address Bit to 0
        bitOffset: 30
        bitWidth: 1
        access: read-write
      - name: NOBYTE
        description: No IBI byte
        bitOffset: 31
        bitWidth: 1
        access: read-write
  - name: MINTSET
    description: Master Interrupt Set Register
    addressOffset: 144
    size: 32
    access: read-write
    resetValue: 0
    resetMask: 573184
    fields:
      - name: SLVSTART
        description: Slave start interrupt enable
        bitOffset: 8
        bitWidth: 1
        access: read-write
      - name: MCTRLDONE
        description: Master control done interrupt enable
        bitOffset: 9
        bitWidth: 1
        access: read-write
      - name: COMPLETE
        description: Completed message interrupt enable
        bitOffset: 10
        bitWidth: 1
        access: read-write
      - name: RXPEND
        description: RX pending interrupt enable
        bitOffset: 11
        bitWidth: 1
        access: read-write
      - name: TXNOTFULL
        description: TX buffer/FIFO is not full interrupt enable
        bitOffset: 12
        bitWidth: 1
        access: read-write
      - name: IBIWON
        description: In-Band Interrupt (IBI) won interrupt enable
        bitOffset: 13
        bitWidth: 1
        access: read-write
      - name: ERRWARN
        description: Error or warning (ERRWARN) interrupt enable
        bitOffset: 15
        bitWidth: 1
        access: read-write
      - name: NOWMASTER
        description: Now master (now this I3C module is a master) interrupt enable
        bitOffset: 19
        bitWidth: 1
        access: read-write
  - name: MINTCLR
    description: Master Interrupt Clear Register
    addressOffset: 148
    size: 32
    access: write-only
    resetValue: 0
    resetMask: 0
    fields:
      - name: SLVSTART
        description: SLVSTART interrupt enable clear
        bitOffset: 8
        bitWidth: 1
        access: write-only
      - name: MCTRLDONE
        description: MCTRLDONE interrupt enable clear
        bitOffset: 9
        bitWidth: 1
        access: write-only
      - name: COMPLETE
        description: COMPLETE interrupt enable clear
        bitOffset: 10
        bitWidth: 1
        access: write-only
      - name: RXPEND
        description: RXPEND interrupt enable clear
        bitOffset: 11
        bitWidth: 1
        access: write-only
      - name: TXNOTFULL
        description: TXNOTFULL interrupt enable clear
        bitOffset: 12
        bitWidth: 1
        access: write-only
      - name: IBIWON
        description: IBIWON interrupt enable clear
        bitOffset: 13
        bitWidth: 1
        access: write-only
      - name: ERRWARN
        description: ERRWARN interrupt enable clear
        bitOffset: 15
        bitWidth: 1
        access: write-only
      - name: NOWMASTER
        description: NOWMASTER interrupt enable clear
        bitOffset: 19
        bitWidth: 1
        access: write-only
  - name: MINTMASKED
    description: Master Interrupt Mask Register
    addressOffset: 152
    size: 32
    access: read-only
    resetValue: 4096
    resetMask: 573184
    fields:
      - name: SLVSTART
        description: SLVSTART interrupt mask
        bitOffset: 8
        bitWidth: 1
        access: read-only
      - name: MCTRLDONE
        description: MCTRLDONE interrupt mask
        bitOffset: 9
        bitWidth: 1
        access: read-only
      - name: COMPLETE
        description: COMPLETE interrupt mask
        bitOffset: 10
        bitWidth: 1
        access: read-only
      - name: RXPEND
        description: RXPEND interrupt mask
        bitOffset: 11
        bitWidth: 1
        access: read-only
      - name: TXNOTFULL
        description: TXNOTFULL interrupt mask
        bitOffset: 12
        bitWidth: 1
        access: read-only
      - name: IBIWON
        description: IBIWON interrupt mask
        bitOffset: 13
        bitWidth: 1
        access: read-only
      - name: ERRWARN
        description: ERRWARN interrupt mask
        bitOffset: 15
        bitWidth: 1
        access: read-only
      - name: NOWMASTER
        description: NOWMASTER interrupt mask
        bitOffset: 19
        bitWidth: 1
        access: read-only
  - name: MERRWARN
    description: Master Errors and Warnings Register
    addressOffset: 156
    size: 32
    access: read-write
    resetValue: 0
    resetMask: 2033180
    fields:
      - name: NACK
        description: Not acknowledge (NACK) error
        bitOffset: 2
        bitWidth: 1
        access: read-write
      - name: WRABT
        description: WRABT (Write abort) error
        bitOffset: 3
        bitWidth: 1
        access: read-write
      - name: TERM
        description: Terminate error
        bitOffset: 4
        bitWidth: 1
        access: read-write
      - name: HPAR
        description: High data rate parity
        bitOffset: 9
        bitWidth: 1
        access: read-write
      - name: HCRC
        description: High data rate CRC error
        bitOffset: 10
        bitWidth: 1
        access: read-write
      - name: OREAD
        description: Over-read error
        bitOffset: 16
        bitWidth: 1
        access: read-write
      - name: OWRITE
        description: Over-write error
        bitOffset: 17
        bitWidth: 1
        access: read-write
      - name: MSGERR
        description: Message error
        bitOffset: 18
        bitWidth: 1
        access: read-write
      - name: INVREQ
        description: Invalid request error
        bitOffset: 19
        bitWidth: 1
        access: read-write
      - name: TIMEOUT
        description: TIMEOUT error
        bitOffset: 20
        bitWidth: 1
        access: read-write
  - name: MDMACTRL
    description: Master DMA Control Register
    addressOffset: 160
    size: 32
    access: read-write
    resetValue: 16
    resetMask: 63
    fields:
      - name: DMAFB
        description: DMA from bus
        bitOffset: 0
        bitWidth: 2
        access: read-write
        enumeratedValues:
          - name: NOT_USED
            description: 'NOT_USED: DMA is not used'
            value: 0
          - name: ENABLE_ONE_FRAME
            description: 'ENABLE_ONE_FRAME: DMA is enabled for 1 frame. DMAFB auto-clears
              on STOP or repeated START. See MCONFIG.MATCHSS.'
            value: 1
          - name: ENABLE
            description: 'ENABLE: DMA is enabled until the DMA is turned off.'
            value: 2
      - name: DMATB
        description: DMA to bus
        bitOffset: 2
        bitWidth: 2
        access: read-write
        enumeratedValues:
          - name: NOT_USED
            description: 'NOT_USED: DMA is not used'
            value: 0
          - name: ENABLE_ONE_FRAME
            description: 'ENABLE_ONE_FRAME: DMA is enabled for 1 frame (ended by DMA
              or Terminated). DMATB auto-clears on STOP or START. See MCONFIG.MATCHSS.'
            value: 1
          - name: ENABLE
            description: 'ENABLE: DMA is enabled until DMA is turned off. Normally
              DMA ENABLE should only be used in Master Message mode.'
            value: 2
      - name: DMAWIDTH
        description: DMA width
        bitOffset: 4
        bitWidth: 2
        access: read-write
        enumeratedValues:
          - name: BYTE
            description: BYTE
            value: 0
          - name: BYTE_AGAIN
            description: BYTE_AGAIN
            value: 1
          - name: HALF_WORD
            description: 'HALF_WORD: Half-word (16 bits). This will make sure that
              2 bytes are free/available in FIFO.'
            value: 2
  - name: MDATACTRL
    description: Master Data Control Register
    addressOffset: 172
    size: 32
    access: read-write
    resetValue: 2147483696
    resetMask: 3743351031
    fields:
      - name: FLUSHTB
        description: Flush to-bus buffer/FIFO
        bitOffset: 0
        bitWidth: 1
        access: write-only
      - name: FLUSHFB
        description: Flush from-bus buffer/FIFO
        bitOffset: 1
        bitWidth: 1
        access: write-only
      - name: UNLOCK
        description: Unlock
        bitOffset: 3
        bitWidth: 1
        access: write-only
      - name: TXTRIG
        description: TX trigger level
        bitOffset: 4
        bitWidth: 2
        access: read-write
      - name: RXTRIG
        description: RX trigger level
        bitOffset: 6
        bitWidth: 2
        access: read-write
      - name: TXCOUNT
        description: TX byte count
        bitOffset: 16
        bitWidth: 5
        access: read-only
      - name: RXCOUNT
        description: RX byte count
        bitOffset: 24
        bitWidth: 5
        access: read-only
      - name: TXFULL
        description: TX is full
        bitOffset: 30
        bitWidth: 1
        access: read-only
      - name: RXEMPTY
        description: RX is empty
        bitOffset: 31
        bitWidth: 1
        access: read-only
  - name: MWDATAB
    description: Master Write Data Byte Register
    addressOffset: 176
    size: 32
    access: write-only
    resetValue: 0
    resetMask: 0
    fields:
      - name: DATA
        description: Data byte
        bitOffset: 0
        bitWidth: 8
        access: write-only
      - name: END
        description: End of message
        bitOffset: 8
        bitWidth: 1
        access: write-only
      - name: END_ALSO
        description: End of message also
        bitOffset: 16
        bitWidth: 1
        access: write-only
  - name: MWDATABE
    description: Master Write Data Byte End Register
    addressOffset: 180
    size: 32
    access: write-only
    resetValue: 0
    resetMask: 0
    fields:
      - name: DATA
        description: Data
        bitOffset: 0
        bitWidth: 8
        access: write-only
  - name: MWDATAH
    description: Master Write Data Half-word Register
    addressOffset: 184
    size: 32
    access: write-only
    resetValue: 0
    resetMask: 0
    fields:
      - name: DATA0
        description: Data byte 0
        bitOffset: 0
        bitWidth: 8
        access: write-only
      - name: DATA1
        description: Data byte 1
        bitOffset: 8
        bitWidth: 8
        access: write-only
      - name: END
        description: End of message
        bitOffset: 16
        bitWidth: 1
        access: write-only
  - name: MWDATAHE
    description: Master Write Data Byte End Register
    addressOffset: 188
    size: 32
    access: write-only
    resetValue: 0
    resetMask: 0
    fields:
      - name: DATA0
        description: DATA 0
        bitOffset: 0
        bitWidth: 8
        access: write-only
      - name: DATA1
        description: DATA 1
        bitOffset: 8
        bitWidth: 8
        access: write-only
  - name: MRDATAB
    description: Master Read Data Byte Register
    addressOffset: 192
    size: 32
    access: read-only
    resetValue: 0
    resetMask: 255
    fields:
      - name: VALUE
        description: VALUE
        bitOffset: 0
        bitWidth: 8
        access: read-only
  - name: MRDATAH
    description: Master Read Data Half-word Register
    addressOffset: 200
    size: 32
    access: read-only
    resetValue: 0
    resetMask: 65535
    fields:
      - name: LSB
        description: LSB
        bitOffset: 0
        bitWidth: 8
        access: read-only
      - name: MSB
        description: MSB
        bitOffset: 8
        bitWidth: 8
        access: read-only
  - name: MWDATAB1
    description: Controller Write Byte Data 1
    addressOffset: 204
    size: 32
    access: read-only
    resetValue: 0
    resetMask: 255
    fields:
      - name: VALUE
        description: VALUE
        bitOffset: 0
        bitWidth: 8
        access: read-only
  - name: MWMSG_SDR_CONTROL
    description: Master Write Message in SDR mode
    alternateGroup: MWMSG_SDR
    addressOffset: 208
    size: 32
    access: write-only
    resetValue: 0
    resetMask: 0
    fields:
      - name: DIR
        description: Direction
        bitOffset: 0
        bitWidth: 1
        access: write-only
        enumeratedValues:
          - name: WRITE
            description: Write
            value: 0
          - name: READ
            description: Read
            value: 1
      - name: ADDR
        description: Address to be written to
        bitOffset: 1
        bitWidth: 7
        access: write-only
      - name: END
        description: End of SDR message
        bitOffset: 8
        bitWidth: 1
        access: write-only
      - name: I2C
        description: I2C
        bitOffset: 10
        bitWidth: 1
        access: write-only
        enumeratedValues:
          - name: I3CMESSAGE
            description: I3C message
            value: 0
          - name: I2CMESSAGE
            description: I2C message
            value: 1
      - name: LEN
        description: Length
        bitOffset: 11
        bitWidth: 5
        access: write-only
  - name: MWMSG_SDR_DATA
    description: Master Write Message Data in SDR mode
    alternateGroup: MWMSG_SDR
    addressOffset: 208
    size: 32
    access: write-only
    resetValue: 0
    resetMask: 4294967295
    fields:
      - name: DATA16B
        description: Data
        bitOffset: 0
        bitWidth: 16
        access: write-only
      - name: END
        description: End of message
        bitOffset: 16
        bitWidth: 1
        access: write-only
  - name: MRMSG_SDR
    description: Master Read Message in SDR mode
    addressOffset: 212
    size: 32
    access: read-only
    resetValue: 0
    resetMask: 65535
    fields:
      - name: DATA
        description: Data
        bitOffset: 0
        bitWidth: 16
        access: read-only
  - name: MWMSG_DDR_CONTROL
    description: Master Write Message in DDR mode
    alternateGroup: MWMSG_DDR
    addressOffset: 216
    size: 32
    access: write-only
    resetValue: 0
    resetMask: 0
    fields:
      - name: LEN
        description: Length of message
        bitOffset: 0
        bitWidth: 10
        access: write-only
      - name: END
        description: End of message
        bitOffset: 14
        bitWidth: 1
        access: write-only
  - name: MWMSG_DDR_DATA
    description: Master Write Message Data in DDR mode
    alternateGroup: MWMSG_DDR
    addressOffset: 216
    size: 32
    access: write-only
    resetValue: 0
    resetMask: 4294967295
    fields:
      - name: DATA16B
        description: Data
        bitOffset: 0
        bitWidth: 16
        access: write-only
      - name: END
        description: End of message
        bitOffset: 16
        bitWidth: 1
        access: write-only
  - name: MRMSG_DDR
    description: Master Read Message in DDR mode
    addressOffset: 220
    size: 32
    access: read-write
    resetValue: 0
    resetMask: 67108863
    fields:
      - name: DATA
        description: Data
        bitOffset: 0
        bitWidth: 16
        access: read-write
      - name: CLEN
        description: Current length
        bitOffset: 16
        bitWidth: 10
        access: read-write
  - name: MDYNADDR
    description: Master Dynamic Address Register
    addressOffset: 228
    size: 32
    access: read-write
    resetValue: 0
    resetMask: 255
    fields:
      - name: DAVALID
        description: Dynamic address valid
        bitOffset: 0
        bitWidth: 1
        access: read-write
      - name: DADDR
        description: Dynamic address
        bitOffset: 1
        bitWidth: 7
        access: read-write
  - name: SID
    description: Slave Module ID Register
    addressOffset: 4092
    size: 32
    access: read-only
    resetValue: 3989504000
    resetMask: 4294967295
    fields:
      - name: ID
        description: ID
        bitOffset: 0
        bitWidth: 32
        access: read-only
interrupts:
  - name: I3C0
addressBlocks:
  - offset: 0
    size: 4096
    usage: registers
