s13n/AES42HAT/fw/model/SWM0.yaml

# Created from LPC865.svd

name: SWM0
description: LPC86x SWM
groupName: SWM
registers:
  - name: PINASSIGN0
    description: Pin assign register 0. Assign movable functions U0_TXD, U0_RXD, U0_RTS,
      U0_CTS.
    alternateGroup: PINASSIGN_PINASSIGN_DATA
    addressOffset: 0
    size: 32
    access: read-write
    resetValue: 4294967295
    resetMask: 4294967295
    fields:
      - name: U0_TXD_O
        description: 'U0_TXD function assignment. The value is the pin number to be
          assigned to this function. The following pins are available: PIO0_0 (= 0)
          to PIO0_31 (= 0x1F) and from PIO1_0 (=0x20) to PIO1_21(=0x35) .'
        bitOffset: 0
        bitWidth: 8
        access: read-write
      - name: U0_RXD_I
        description: 'U0_RXD function assignment. The value is the pin number to be
          assigned to this function. The following pins are available: PIO0_0 (= 0)
          to PIO0_31 (= 0x1F) and from PIO1_0 (=0x20) to PIO1_21(=0x35).'
        bitOffset: 8
        bitWidth: 8
        access: read-write
      - name: U0_RTS_O
        description: 'U0_RTS function assignment. The value is the pin number to be
          assigned to this function. The following pins are available: PIO0_0 (= 0)
          to PIO0_31 (= 0x1F) and from PIO1_0 (=0x20) to PIO1_21(=0x35).'
        bitOffset: 16
        bitWidth: 8
        access: read-write
      - name: U0_CTS_I
        description: 'U0_CTS function assignment. The value is the pin number to be
          assigned to this function. The following pins are available: PIO0_0 (= 0)
          to PIO0_31 (= 0x1F) and from PIO1_0 (=0x20) to PIO1_21(=0x35).'
        bitOffset: 24
        bitWidth: 8
        access: read-write
  - name: PINASSIGN_DATA0
    description: Pin assign register
    alternateGroup: PINASSIGN_PINASSIGN_DATA
    addressOffset: 0
    size: 32
    access: read-write
    resetValue: 4294967295
    resetMask: 4294967295
    fields:
      - name: DATA0
        description: 'T0_MAT3 function assignment. The value is the pin number to
          be assigned to this function. The following pins are available: PIO0_0 (=
          0) to PIO0_31 (= 0x1F) and from PIO1_0 (=0x20) to PIO1_21(=0x35).'
        bitOffset: 0
        bitWidth: 8
        access: read-write
      - name: DATA1
        description: 'T0_CAP0 function assignment. The value is the pin number to
          be assigned to this function. The following pins are available: PIO0_0 (=
          0) to PIO0_31 (= 0x1F) and from PIO1_0 (=0x20) to PIO1_21(=0x35).'
        bitOffset: 8
        bitWidth: 8
        access: read-write
      - name: DATA2
        description: 'T0_CAP1 function assignment. The value is the pin number to
          be assigned to this function. The following pins are available: PIO0_0 (=
          0) to PIO0_31 (= 0x1F) and from PIO1_0 (=0x20) to PIO1_21(=0x35).'
        bitOffset: 16
        bitWidth: 8
        access: read-write
      - name: DATA3
        description: 'T0_CAP2 function assignment. The value is the pin number to
          be assigned to this function. The following pins are available: PIO0_0 (=
          0) to PIO0_31 (= 0x1F) and from PIO1_0 (=0x20) to PIO1_21(=0x35).'
        bitOffset: 24
        bitWidth: 8
        access: read-write
  - name: PINASSIGN1
    description: Pin assign register 1. Assign movable functions U0_SCLK, U1_TXD,
      U1_RXD, U1_RTS.
    alternateGroup: PINASSIGN_PINASSIGN_DATA
    addressOffset: 4
    size: 32
    access: read-write
    resetValue: 4294967295
    resetMask: 4294967295
    fields:
      - name: U0_SCLK_IO
        description: 'U0_SCLK function assignment. The value is the pin number to
          be assigned to this function. The following pins are available: PIO0_0 (=
          0) to PIO0_31 (= 0x1F) and from PIO1_0 (=0x20) to PIO1_21(=0x35).'
        bitOffset: 0
        bitWidth: 8
        access: read-write
      - name: U1_TXD_O
        description: 'U1_TXD function assignment. The value is the pin number to be
          assigned to this function. The following pins are available: PIO0_0 (= 0)
          to PIO0_31 (= 0x1F) and from PIO1_0 (=0x20) to PIO1_21(=0x35).'
        bitOffset: 8
        bitWidth: 8
        access: read-write
      - name: U1_RXD_I
        description: 'U1_RXD function assignment. The value is the pin number to be
          assigned to this function. The following pins are available: PIO0_0 (= 0)
          to PIO0_31 (= 0x1F) and from PIO1_0 (=0x20) to PIO1_21(=0x35).'
        bitOffset: 16
        bitWidth: 8
        access: read-write
      - name: U1_RTS_O
        description: 'U1_RTS function assignment. The value is the pin number to be
          assigned to this function. The following pins are available: PIO0_0 (= 0)
          to PIO0_31 (= 0x1F) and from PIO1_0 (=0x20) to PIO1_21(=0x35).'
        bitOffset: 24
        bitWidth: 8
        access: read-write
  - name: PINASSIGN_DATA1
    description: Pin assign register
    alternateGroup: PINASSIGN_PINASSIGN_DATA
    addressOffset: 4
    size: 32
    access: read-write
    resetValue: 4294967295
    resetMask: 4294967295
    fields:
      - name: DATA0
        description: 'T0_MAT3 function assignment. The value is the pin number to
          be assigned to this function. The following pins are available: PIO0_0 (=
          0) to PIO0_31 (= 0x1F) and from PIO1_0 (=0x20) to PIO1_21(=0x35).'
        bitOffset: 0
        bitWidth: 8
        access: read-write
      - name: DATA1
        description: 'T0_CAP0 function assignment. The value is the pin number to
          be assigned to this function. The following pins are available: PIO0_0 (=
          0) to PIO0_31 (= 0x1F) and from PIO1_0 (=0x20) to PIO1_21(=0x35).'
        bitOffset: 8
        bitWidth: 8
        access: read-write
      - name: DATA2
        description: 'T0_CAP1 function assignment. The value is the pin number to
          be assigned to this function. The following pins are available: PIO0_0 (=
          0) to PIO0_31 (= 0x1F) and from PIO1_0 (=0x20) to PIO1_21(=0x35).'
        bitOffset: 16
        bitWidth: 8
        access: read-write
      - name: DATA3
        description: 'T0_CAP2 function assignment. The value is the pin number to
          be assigned to this function. The following pins are available: PIO0_0 (=
          0) to PIO0_31 (= 0x1F) and from PIO1_0 (=0x20) to PIO1_21(=0x35).'
        bitOffset: 24
        bitWidth: 8
        access: read-write
  - name: PINASSIGN2
    description: Pin assign register 2. Assign movable functions U1_CTS, U1_SCLK,
      U2_TXD, U2_RXD.
    alternateGroup: PINASSIGN_PINASSIGN_DATA
    addressOffset: 8
    size: 32
    access: read-write
    resetValue: 4294967295
    resetMask: 4294967295
    fields:
      - name: U1_CTS_I
        description: 'U1_CTS function assignment. The value is the pin number to be
          assigned to this function. The following pins are available: PIO0_0 (= 0)
          to PIO0_31 (= 0x1F) and from PIO1_0 (=0x20) to PIO1_21(=0x35).'
        bitOffset: 0
        bitWidth: 8
        access: read-write
      - name: U1_SCLK_IO
        description: 'U1_SCLK function assignment. The value is the pin number to
          be assigned to this function. The following pins are available: PIO0_0 (=
          0) to PIO0_31 (= 0x1F) and from PIO1_0 (=0x20) to PIO1_21(=0x35).'
        bitOffset: 8
        bitWidth: 8
        access: read-write
      - name: U2_TXD_O
        description: 'U2_TXD function assignment. The value is the pin number to be
          assigned to this function. The following pins are available: PIO0_0 (= 0)
          to PIO0_31 (= 0x1F) and from PIO1_0 (=0x20) to PIO1_21(=0x35).'
        bitOffset: 16
        bitWidth: 8
        access: read-write
      - name: U2_RXD_I
        description: 'U2_RXD function assignment. The value is the pin number to be
          assigned to this function. The following pins are available: PIO0_0 (= 0)
          to PIO0_31 (= 0x1F) and from PIO1_0 (=0x20) to PIO1_21(=0x35).'
        bitOffset: 24
        bitWidth: 8
        access: read-write
  - name: PINASSIGN_DATA2
    description: Pin assign register
    alternateGroup: PINASSIGN_PINASSIGN_DATA
    addressOffset: 8
    size: 32
    access: read-write
    resetValue: 4294967295
    resetMask: 4294967295
    fields:
      - name: DATA0
        description: 'T0_MAT3 function assignment. The value is the pin number to
          be assigned to this function. The following pins are available: PIO0_0 (=
          0) to PIO0_31 (= 0x1F) and from PIO1_0 (=0x20) to PIO1_21(=0x35).'
        bitOffset: 0
        bitWidth: 8
        access: read-write
      - name: DATA1
        description: 'T0_CAP0 function assignment. The value is the pin number to
          be assigned to this function. The following pins are available: PIO0_0 (=
          0) to PIO0_31 (= 0x1F) and from PIO1_0 (=0x20) to PIO1_21(=0x35).'
        bitOffset: 8
        bitWidth: 8
        access: read-write
      - name: DATA2
        description: 'T0_CAP1 function assignment. The value is the pin number to
          be assigned to this function. The following pins are available: PIO0_0 (=
          0) to PIO0_31 (= 0x1F) and from PIO1_0 (=0x20) to PIO1_21(=0x35).'
        bitOffset: 16
        bitWidth: 8
        access: read-write
      - name: DATA3
        description: 'T0_CAP2 function assignment. The value is the pin number to
          be assigned to this function. The following pins are available: PIO0_0 (=
          0) to PIO0_31 (= 0x1F) and from PIO1_0 (=0x20) to PIO1_21(=0x35).'
        bitOffset: 24
        bitWidth: 8
        access: read-write
  - name: PINASSIGN3
    description: Pin assign register 3. Assign movable function U2_RTS, U2_CTS, U2_SCLK,
      SPI0_SCK.
    alternateGroup: PINASSIGN_PINASSIGN_DATA
    addressOffset: 12
    size: 32
    access: read-write
    resetValue: 4294967295
    resetMask: 4294967295
    fields:
      - name: U2_RTS_O
        description: 'U2_RTS function assignment. The value is the pin number to be
          assigned to this function. The following pins are available: PIO0_0 (= 0)
          to PIO0_31 (= 0x1F) and from PIO1_0 (=0x20) to PIO1_21(=0x35).'
        bitOffset: 0
        bitWidth: 8
        access: read-write
      - name: U2_CTS_I
        description: 'U2_CTS function assignment. The value is the pin number to be
          assigned to this function. The following pins are available: PIO0_0 (= 0)
          to PIO0_31 (= 0x1F) and from PIO1_0 (=0x20) to PIO1_21(=0x35).'
        bitOffset: 8
        bitWidth: 8
        access: read-write
      - name: U2_SCLK_IO
        description: 'U2_SCLK function assignment. The value is the pin number to
          be assigned to this function. The following pins are available: PIO0_0 (=
          0) to PIO0_31 (= 0x1F) and from PIO1_0 (=0x20) to PIO1_21(=0x35).'
        bitOffset: 16
        bitWidth: 8
        access: read-write
      - name: SPI0_SCK_IO
        description: 'SPI0_SCK function assignment. The value is the pin number to
          be assigned to this function. The following pins are available: PIO0_0 (=
          0) to PIO0_31 (= 0x1F) and from PIO1_0 (=0x20) to PIO1_21(=0x35).'
        bitOffset: 24
        bitWidth: 8
        access: read-write
  - name: PINASSIGN_DATA3
    description: Pin assign register
    alternateGroup: PINASSIGN_PINASSIGN_DATA
    addressOffset: 12
    size: 32
    access: read-write
    resetValue: 4294967295
    resetMask: 4294967295
    fields:
      - name: DATA0
        description: 'T0_MAT3 function assignment. The value is the pin number to
          be assigned to this function. The following pins are available: PIO0_0 (=
          0) to PIO0_31 (= 0x1F) and from PIO1_0 (=0x20) to PIO1_21(=0x35).'
        bitOffset: 0
        bitWidth: 8
        access: read-write
      - name: DATA1
        description: 'T0_CAP0 function assignment. The value is the pin number to
          be assigned to this function. The following pins are available: PIO0_0 (=
          0) to PIO0_31 (= 0x1F) and from PIO1_0 (=0x20) to PIO1_21(=0x35).'
        bitOffset: 8
        bitWidth: 8
        access: read-write
      - name: DATA2
        description: 'T0_CAP1 function assignment. The value is the pin number to
          be assigned to this function. The following pins are available: PIO0_0 (=
          0) to PIO0_31 (= 0x1F) and from PIO1_0 (=0x20) to PIO1_21(=0x35).'
        bitOffset: 16
        bitWidth: 8
        access: read-write
      - name: DATA3
        description: 'T0_CAP2 function assignment. The value is the pin number to
          be assigned to this function. The following pins are available: PIO0_0 (=
          0) to PIO0_31 (= 0x1F) and from PIO1_0 (=0x20) to PIO1_21(=0x35).'
        bitOffset: 24
        bitWidth: 8
        access: read-write
  - name: PINASSIGN4
    description: Pin assign register 4. Assign movable functions SPI0_MOSI, SPI0_MISO,
      SPI0_SSEL0, SPI0_SSEL1.
    alternateGroup: PINASSIGN_PINASSIGN_DATA
    addressOffset: 16
    size: 32
    access: read-write
    resetValue: 4294967295
    resetMask: 4294967295
    fields:
      - name: SPI0_MOSI_IO
        description: 'SPI0_MOSI function assignment. The value is the pin number to
          be assigned to this function. The following pins are available: PIO0_0 (=
          0) to PIO0_31 (= 0x1F) and from PIO1_0 (=0x20) to PIO1_21(=0x35).'
        bitOffset: 0
        bitWidth: 8
        access: read-write
      - name: SPI0_MISO_IO
        description: 'SPI0_MISIO function assignment. The value is the pin number
          to be assigned to this function. The following pins are available: PIO0_0
          (= 0) to PIO0_31 (= 0x1F) and from PIO1_0 (=0x20) to PIO1_21(=0x35).'
        bitOffset: 8
        bitWidth: 8
        access: read-write
      - name: SPI0_SSEL0_IO
        description: 'SPI0_SSEL0 function assignment. The value is the pin number
          to be assigned to this function. The following pins are available: PIO0_0
          (= 0) to PIO0_31 (= 0x1F) and from PIO1_0 (=0x20) to PIO1_21(=0x35).'
        bitOffset: 16
        bitWidth: 8
        access: read-write
      - name: SPI0_SSEL1_IO
        description: 'SPI0_SSEL1 function assignment. The value is the pin number
          to be assigned to this function. The following pins are available: PIO0_0
          (= 0) to PIO0_31 (= 0x1F) and from PIO1_0 (=0x20) to PIO1_21(=0x35).'
        bitOffset: 24
        bitWidth: 8
        access: read-write
  - name: PINASSIGN_DATA4
    description: Pin assign register
    alternateGroup: PINASSIGN_PINASSIGN_DATA
    addressOffset: 16
    size: 32
    access: read-write
    resetValue: 4294967295
    resetMask: 4294967295
    fields:
      - name: DATA0
        description: 'T0_MAT3 function assignment. The value is the pin number to
          be assigned to this function. The following pins are available: PIO0_0 (=
          0) to PIO0_31 (= 0x1F) and from PIO1_0 (=0x20) to PIO1_21(=0x35).'
        bitOffset: 0
        bitWidth: 8
        access: read-write
      - name: DATA1
        description: 'T0_CAP0 function assignment. The value is the pin number to
          be assigned to this function. The following pins are available: PIO0_0 (=
          0) to PIO0_31 (= 0x1F) and from PIO1_0 (=0x20) to PIO1_21(=0x35).'
        bitOffset: 8
        bitWidth: 8
        access: read-write
      - name: DATA2
        description: 'T0_CAP1 function assignment. The value is the pin number to
          be assigned to this function. The following pins are available: PIO0_0 (=
          0) to PIO0_31 (= 0x1F) and from PIO1_0 (=0x20) to PIO1_21(=0x35).'
        bitOffset: 16
        bitWidth: 8
        access: read-write
      - name: DATA3
        description: 'T0_CAP2 function assignment. The value is the pin number to
          be assigned to this function. The following pins are available: PIO0_0 (=
          0) to PIO0_31 (= 0x1F) and from PIO1_0 (=0x20) to PIO1_21(=0x35).'
        bitOffset: 24
        bitWidth: 8
        access: read-write
  - name: PINASSIGN5
    description: Pin assign register 5. Assign movable functions SPI0_SSEL2, SPI0_SSEL3,
      SPI1_SCK, SPI1_MOSI
    alternateGroup: PINASSIGN_PINASSIGN_DATA
    addressOffset: 20
    size: 32
    access: read-write
    resetValue: 4294967295
    resetMask: 4294967295
    fields:
      - name: SPI0_SSEL2_IO
        description: 'SPI0_SSEL2 function assignment. The value is the pin number
          to be assigned to this function. The following pins are available: PIO0_0
          (= 0) to PIO0_31 (= 0x1F) and from PIO1_0 (=0x20) to PIO1_21(=0x35).'
        bitOffset: 0
        bitWidth: 8
        access: read-write
      - name: SPI0_SSEL3_IO
        description: 'SPI0_SSEL3 function assignment. The value is the pin number
          to be assigned to this function. The following pins are available: PIO0_0
          (= 0) to PIO0_31 (= 0x1F) and from PIO1_0 (=0x20) to PIO1_21(=0x35).'
        bitOffset: 8
        bitWidth: 8
        access: read-write
      - name: SPI1_SCK_IO
        description: 'SPI1_SCK function assignment. The value is the pin number to
          be assigned to this function. The following pins are available: PIO0_0 (=
          0) to PIO0_31 (= 0x1F) and from PIO1_0 (=0x20) to PIO1_21(=0x35).'
        bitOffset: 16
        bitWidth: 8
        access: read-write
      - name: SPI1_MOSI_IO
        description: 'SPI1_MOSI function assignment. The value is the pin number to
          be assigned to this function. The following pins are available: PIO0_0 (=
          0) to PIO0_31 (= 0x1F) and from PIO1_0 (=0x20) to PIO1_21(=0x35).'
        bitOffset: 24
        bitWidth: 8
        access: read-write
  - name: PINASSIGN_DATA5
    description: Pin assign register
    alternateGroup: PINASSIGN_PINASSIGN_DATA
    addressOffset: 20
    size: 32
    access: read-write
    resetValue: 4294967295
    resetMask: 4294967295
    fields:
      - name: DATA0
        description: 'T0_MAT3 function assignment. The value is the pin number to
          be assigned to this function. The following pins are available: PIO0_0 (=
          0) to PIO0_31 (= 0x1F) and from PIO1_0 (=0x20) to PIO1_21(=0x35).'
        bitOffset: 0
        bitWidth: 8
        access: read-write
      - name: DATA1
        description: 'T0_CAP0 function assignment. The value is the pin number to
          be assigned to this function. The following pins are available: PIO0_0 (=
          0) to PIO0_31 (= 0x1F) and from PIO1_0 (=0x20) to PIO1_21(=0x35).'
        bitOffset: 8
        bitWidth: 8
        access: read-write
      - name: DATA2
        description: 'T0_CAP1 function assignment. The value is the pin number to
          be assigned to this function. The following pins are available: PIO0_0 (=
          0) to PIO0_31 (= 0x1F) and from PIO1_0 (=0x20) to PIO1_21(=0x35).'
        bitOffset: 16
        bitWidth: 8
        access: read-write
      - name: DATA3
        description: 'T0_CAP2 function assignment. The value is the pin number to
          be assigned to this function. The following pins are available: PIO0_0 (=
          0) to PIO0_31 (= 0x1F) and from PIO1_0 (=0x20) to PIO1_21(=0x35).'
        bitOffset: 24
        bitWidth: 8
        access: read-write
  - name: PINASSIGN6
    description: Pin assign register 6. Assign movable functions SPI1_MISO, SPI1_SSEL0,
      SPI1_SSEL1, SCT0_IN0.
    alternateGroup: PINASSIGN_PINASSIGN_DATA
    addressOffset: 24
    size: 32
    access: read-write
    resetValue: 4294967295
    resetMask: 4294967295
    fields:
      - name: SPI1_MISO_IO
        description: 'SPI1_MISO function assignment. The value is the pin number to
          be assigned to this function. The following pins are available: PIO0_0 (=
          0) to PIO0_31 (= 0x1F) and from PIO1_0 (=0x20) to PIO1_21(=0x35).'
        bitOffset: 0
        bitWidth: 8
        access: read-write
      - name: SPI1_SSEL0_IO
        description: 'SPI1_SSEL0 function assignment. The value is the pin number
          to be assigned to this function. The following pins are available: PIO0_0
          (= 0) to PIO0_31 (= 0x1F) and from PIO1_0 (=0x20) to PIO1_21(=0x35).'
        bitOffset: 8
        bitWidth: 8
        access: read-write
      - name: SPI1_SSEL1_IO
        description: 'SPI1_SSEL1 function assignment. The value is the pin number
          to be assigned to this function. The following pins are available: PIO0_0
          (= 0) to PIO0_31 (= 0x1F) and from PIO1_0 (=0x20) to PIO1_21(=0x35).'
        bitOffset: 16
        bitWidth: 8
        access: read-write
      - name: I2C0_SDA_IO
        description: 'I2C0_SDA_IO function assignment. The value is the pin number
          to be assigned to this function. The following pins are available: PIO0_0
          (= 0) to PIO0_31 (= 0x1F) and from PIO1_0 (=0x20) to PIO1_21(=0x35).'
        bitOffset: 24
        bitWidth: 8
        access: read-write
  - name: PINASSIGN_DATA6
    description: Pin assign register
    alternateGroup: PINASSIGN_PINASSIGN_DATA
    addressOffset: 24
    size: 32
    access: read-write
    resetValue: 4294967295
    resetMask: 4294967295
    fields:
      - name: DATA0
        description: 'T0_MAT3 function assignment. The value is the pin number to
          be assigned to this function. The following pins are available: PIO0_0 (=
          0) to PIO0_31 (= 0x1F) and from PIO1_0 (=0x20) to PIO1_21(=0x35).'
        bitOffset: 0
        bitWidth: 8
        access: read-write
      - name: DATA1
        description: 'T0_CAP0 function assignment. The value is the pin number to
          be assigned to this function. The following pins are available: PIO0_0 (=
          0) to PIO0_31 (= 0x1F) and from PIO1_0 (=0x20) to PIO1_21(=0x35).'
        bitOffset: 8
        bitWidth: 8
        access: read-write
      - name: DATA2
        description: 'T0_CAP1 function assignment. The value is the pin number to
          be assigned to this function. The following pins are available: PIO0_0 (=
          0) to PIO0_31 (= 0x1F) and from PIO1_0 (=0x20) to PIO1_21(=0x35).'
        bitOffset: 16
        bitWidth: 8
        access: read-write
      - name: DATA3
        description: 'T0_CAP2 function assignment. The value is the pin number to
          be assigned to this function. The following pins are available: PIO0_0 (=
          0) to PIO0_31 (= 0x1F) and from PIO1_0 (=0x20) to PIO1_21(=0x35).'
        bitOffset: 24
        bitWidth: 8
        access: read-write
  - name: PINASSIGN7
    description: Pin assign register 7. Assign movable functions SCT_IN1, SCT_IN2,
      SCT_IN3, SCT_OUT0.
    alternateGroup: PINASSIGN_PINASSIGN_DATA
    addressOffset: 28
    size: 32
    access: read-write
    resetValue: 4294967295
    resetMask: 4294967295
    fields:
      - name: I2C0_SCL_IO
        description: 'I2C0_SCL_IO function assignment. The value is the pin number
          to be assigned to this function. The following pins are available: PIO0_0
          (= 0) to PIO0_31 (= 0x1F) and from PIO1_0 (=0x20) to PIO1_21(=0x35).'
        bitOffset: 0
        bitWidth: 8
        access: read-write
      - name: I3C0_SDA_IO
        description: 'I3C0_SDA_IO function assignment. The value is the pin number
          to be assigned to this function. The following pins are available: PIO0_0
          (= 0) to PIO0_31 (= 0x1F) and from PIO1_0 (=0x20) to PIO1_21(=0x35).'
        bitOffset: 8
        bitWidth: 8
        access: read-write
      - name: I3C0_SCL_IO
        description: 'I3C0_SCL_IO function assignment. The value is the pin number
          to be assigned to this function. The following pins are available: PIO0_0
          (= 0) to PIO0_31 (= 0x1F) and from PIO1_0 (=0x20) to PIO1_21(=0x35).'
        bitOffset: 16
        bitWidth: 8
        access: read-write
      - name: I3C0_PUR_IO
        description: 'I3C0_PUR_IO function assignment. The value is the pin number
          to be assigned to this function. The following pins are available: PIO0_0
          (= 0) to PIO0_31 (= 0x1F) and from PIO1_0 (=0x20) to PIO1_21(=0x35).'
        bitOffset: 24
        bitWidth: 8
        access: read-write
  - name: PINASSIGN_DATA7
    description: Pin assign register
    alternateGroup: PINASSIGN_PINASSIGN_DATA
    addressOffset: 28
    size: 32
    access: read-write
    resetValue: 4294967295
    resetMask: 4294967295
    fields:
      - name: DATA0
        description: 'T0_MAT3 function assignment. The value is the pin number to
          be assigned to this function. The following pins are available: PIO0_0 (=
          0) to PIO0_31 (= 0x1F) and from PIO1_0 (=0x20) to PIO1_21(=0x35).'
        bitOffset: 0
        bitWidth: 8
        access: read-write
      - name: DATA1
        description: 'T0_CAP0 function assignment. The value is the pin number to
          be assigned to this function. The following pins are available: PIO0_0 (=
          0) to PIO0_31 (= 0x1F) and from PIO1_0 (=0x20) to PIO1_21(=0x35).'
        bitOffset: 8
        bitWidth: 8
        access: read-write
      - name: DATA2
        description: 'T0_CAP1 function assignment. The value is the pin number to
          be assigned to this function. The following pins are available: PIO0_0 (=
          0) to PIO0_31 (= 0x1F) and from PIO1_0 (=0x20) to PIO1_21(=0x35).'
        bitOffset: 16
        bitWidth: 8
        access: read-write
      - name: DATA3
        description: 'T0_CAP2 function assignment. The value is the pin number to
          be assigned to this function. The following pins are available: PIO0_0 (=
          0) to PIO0_31 (= 0x1F) and from PIO1_0 (=0x20) to PIO1_21(=0x35).'
        bitOffset: 24
        bitWidth: 8
        access: read-write
  - name: PINASSIGN8
    description: Pin assign register 8. Assign movable functions ACMP0_OUT, CLKOUT,
      GPIOINT_BMATCH.
    alternateGroup: PINASSIGN_PINASSIGN_DATA
    addressOffset: 32
    size: 32
    access: read-write
    resetValue: 4294967295
    resetMask: 4294967295
    fields:
      - name: ACMP0_OUT_O
        description: 'ACMP0_OUT function assignment. The value is the pin number to
          be assigned to this function. The following pins are available: PIO0_0 (=
          0) to PIO0_31 (= 0x1F) and from PIO1_0 (=0x20) to PIO1_21(=0x35).'
        bitOffset: 0
        bitWidth: 8
        access: read-write
      - name: CLKOUT_O
        description: 'CLKOUT function assignment. The value is the pin number to be
          assigned to this function. The following pins are available: PIO0_0 (= 0)
          to PIO0_31 (= 0x1F) and from PIO1_0 (=0x20) to PIO1_21(=0x35).'
        bitOffset: 8
        bitWidth: 8
        access: read-write
      - name: GPIO_INT_BMAT_O
        description: 'GPIO_INT_BMAT function assignment. The value is the pin number
          to be assigned to this function. The following pins are available: PIO0_0
          (= 0) to PIO0_31 (= 0x1F) and from PIO1_0 (=0x20) to PIO1_21(=0x35).'
        bitOffset: 16
        bitWidth: 8
        access: read-write
  - name: PINASSIGN_DATA8
    description: Pin assign register
    alternateGroup: PINASSIGN_PINASSIGN_DATA
    addressOffset: 32
    size: 32
    access: read-write
    resetValue: 4294967295
    resetMask: 4294967295
    fields:
      - name: DATA0
        description: 'T0_MAT3 function assignment. The value is the pin number to
          be assigned to this function. The following pins are available: PIO0_0 (=
          0) to PIO0_31 (= 0x1F) and from PIO1_0 (=0x20) to PIO1_21(=0x35).'
        bitOffset: 0
        bitWidth: 8
        access: read-write
      - name: DATA1
        description: 'T0_CAP0 function assignment. The value is the pin number to
          be assigned to this function. The following pins are available: PIO0_0 (=
          0) to PIO0_31 (= 0x1F) and from PIO1_0 (=0x20) to PIO1_21(=0x35).'
        bitOffset: 8
        bitWidth: 8
        access: read-write
      - name: DATA2
        description: 'T0_CAP1 function assignment. The value is the pin number to
          be assigned to this function. The following pins are available: PIO0_0 (=
          0) to PIO0_31 (= 0x1F) and from PIO1_0 (=0x20) to PIO1_21(=0x35).'
        bitOffset: 16
        bitWidth: 8
        access: read-write
      - name: DATA3
        description: 'T0_CAP2 function assignment. The value is the pin number to
          be assigned to this function. The following pins are available: PIO0_0 (=
          0) to PIO0_31 (= 0x1F) and from PIO1_0 (=0x20) to PIO1_21(=0x35).'
        bitOffset: 24
        bitWidth: 8
        access: read-write
  - name: FTM_PINASSIGN0
    description: FlexTimer Pin assign register 0 Assign movable functions.
    addressOffset: 384
    size: 32
    access: read-write
    resetValue: 0
    resetMask: 0
    fields:
      - name: FTM0_EXTCLK
        description: Assign movable function FTM0_EXTCLK 00 = Selection 0 function
          pins 01 = Selection 1 function pins 10 = Selection 2 function pins 11 =
          Selection 3 function pins
        bitOffset: 0
        bitWidth: 2
        access: read-write
      - name: FTM0_CH0
        description: Assign movable function FTM0_CH0
        bitOffset: 2
        bitWidth: 2
        access: read-write
      - name: FTM0_CH1
        description: Assign movable function FTM0_CH1
        bitOffset: 4
        bitWidth: 2
        access: read-write
      - name: FTM0_CH2
        description: Assign movable function FTM0_CH2
        bitOffset: 6
        bitWidth: 2
        access: read-write
      - name: FTM0_CH3
        description: Assign movable function FTM0_CH3
        bitOffset: 8
        bitWidth: 2
        access: read-write
      - name: FTM0_CH4
        description: Assign movable function FTM0_CH4
        bitOffset: 10
        bitWidth: 2
        access: read-write
      - name: FTM0_CH5
        description: Assign movable function FTM0_CH5
        bitOffset: 12
        bitWidth: 2
        access: read-write
      - name: FTM0_FAULT0
        description: Assign movable function FTM0_FAULT0
        bitOffset: 14
        bitWidth: 2
        access: read-write
      - name: FTM0_FAULT1
        description: Assign movable function FTM0_FAULT1
        bitOffset: 16
        bitWidth: 2
        access: read-write
      - name: FTM0_FAULT2
        description: Assign movable function FTM0_FAULT2
        bitOffset: 18
        bitWidth: 2
        access: read-write
      - name: FTM0_FAULT3
        description: Assign movable function FTM0_FAULT3
        bitOffset: 20
        bitWidth: 2
        access: read-write
      - name: FTM1_EXTCLK
        description: Assign movable function FTM1_EXTCLK
        bitOffset: 22
        bitWidth: 2
        access: read-write
      - name: FTM1_CH0
        description: Assign movable function FTM1_CH0
        bitOffset: 24
        bitWidth: 2
        access: read-write
      - name: FTM1_CH1
        description: Assign movable function FTM1_CH1
        bitOffset: 26
        bitWidth: 2
        access: read-write
      - name: FTM1_CH2
        description: Assign movable function FTM1_CH2
        bitOffset: 28
        bitWidth: 2
        access: read-write
      - name: FTM1_CH3
        description: Assign movable function FTM1_CH3
        bitOffset: 30
        bitWidth: 2
        access: read-write
  - name: FTM_PINASSIGN1
    description: FlexTimer Pin assign register 0 Assign movable functions.
    addressOffset: 388
    size: 32
    access: read-write
    resetValue: 0
    resetMask: 0
    fields:
      - name: FTM1_QD_PHA
        description: Assign movable function FTM1_QD_PHA
        bitOffset: 0
        bitWidth: 2
        access: read-write
      - name: FTM1_QD_PHB
        description: Assign movable function FTM1_QD_PHB
        bitOffset: 2
        bitWidth: 2
        access: read-write
  - name: PINENABLE0
    description: Pin enable register 0. Enables fixed-pin functions ACMP_I0, ACMP_I1,
      SWCLK, SWDIO, XTALIN, XTALOUT, RESET, CLKIN, VDDCMP and so on.
    addressOffset: 448
    size: 32
    access: read-write
    resetValue: 16776991
    resetMask: 16777215
    fields:
      - name: ACMP_I1
        description: ACMP_I1 function select.
        bitOffset: 0
        bitWidth: 1
        access: read-write
        enumeratedValues:
          - name: ENABLED
            description: ACMP_I1 enabled on pin PIO0_00.
            value: 0
          - name: DISABLED
            description: ACMP_I1 disabled.
            value: 1
      - name: ACMP_I2
        description: ACMP_I2 function select.
        bitOffset: 1
        bitWidth: 1
        access: read-write
        enumeratedValues:
          - name: ACMP_I2_0
            description: ACMP_I2 enabled on pin PIO0_1.
            value: 0
          - name: ACMP_I2_1
            description: ACMP_I2 disabled.
            value: 1
      - name: ACMP_I3
        description: ACMP_I3 function select.
        bitOffset: 2
        bitWidth: 1
        access: read-write
        enumeratedValues:
          - name: ENABLED
            description: ACMP_I3 enabled on pin PIO0_14.
            value: 0
          - name: DISABLED
            description: ACMP_I3 disabled.
            value: 1
      - name: ACMP_I4
        description: ACMP_I4 function select.
        bitOffset: 3
        bitWidth: 1
        access: read-write
        enumeratedValues:
          - name: ENABLED
            description: ACMP_I4 enabled on pin PIO0_23.
            value: 0
          - name: DISABLED
            description: ACMP_I4 disabled.
            value: 1
      - name: ACMP_I5
        description: ACMP_I5 function select.
        bitOffset: 4
        bitWidth: 1
        access: read-write
        enumeratedValues:
          - name: ENABLED
            description: ACMP_I5 enabled on pin PIO0_30.
            value: 0
          - name: DISABLED
            description: ACMP_I5 disabled.
            value: 1
      - name: SWCLK
        description: SWCLK function select.
        bitOffset: 5
        bitWidth: 1
        access: read-write
        enumeratedValues:
          - name: ENABLED
            description: SWCLK enabled on pin PIO0_3.
            value: 0
          - name: DISABLED
            description: SWCLK disabled.
            value: 1
      - name: SWDIO
        description: SWDIO function select.
        bitOffset: 6
        bitWidth: 1
        access: read-write
        enumeratedValues:
          - name: ENABLED
            description: SWDIO enabled on pin PIO0_2.
            value: 0
          - name: DISABLED
            description: SWDIO disabled.
            value: 1
      - name: RESETN
        description: RESETN function select.
        bitOffset: 7
        bitWidth: 1
        access: read-write
        enumeratedValues:
          - name: ENABLED
            description: RESETN enabled on pin PIO0_5.
            value: 0
          - name: DISABLED
            description: RESETN disabled.
            value: 1
      - name: CLKIN
        description: CLKIN function select.
        bitOffset: 8
        bitWidth: 1
        access: read-write
        enumeratedValues:
          - name: CLKIN
            description: CLKIN enabled on pin PIO0_1.
            value: 0
          - name: DISABLED
            description: CLKIN disabled.
            value: 1
      - name: CMPVREF
        description: CMPVREF function select.
        bitOffset: 9
        bitWidth: 1
        access: read-write
        enumeratedValues:
          - name: ENABLED
            description: CMPVREF enabled on pin PIO0_6.
            value: 0
          - name: DISABLED
            description: CMPVREF disabled.
            value: 1
      - name: XTALIN
        description: XTALIN function select.
        bitOffset: 10
        bitWidth: 1
        access: read-write
        enumeratedValues:
          - name: ENABLED
            description: XTALIN enabled on pin PIO0_8.
            value: 0
          - name: DISABLED
            description: XTALIN disabled.
            value: 1
      - name: XTALOUT
        description: XTALOUT function select.
        bitOffset: 11
        bitWidth: 1
        access: read-write
        enumeratedValues:
          - name: ENABLED
            description: XTALOUT enabled on pin PIO0_9.
            value: 0
          - name: DISABLED
            description: XTALOUT disabled.
            value: 1
      - name: ADC_0
        description: ADC_0 function select.
        bitOffset: 12
        bitWidth: 1
        access: read-write
        enumeratedValues:
          - name: ENABLED
            description: ADC_0 enabled on pin PIO0_7.
            value: 0
          - name: DISABLED
            description: ADC_0 disabled.
            value: 1
      - name: ADC_1
        description: ADC_1 function select.
        bitOffset: 13
        bitWidth: 1
        access: read-write
        enumeratedValues:
          - name: ENABLED
            description: ADC_1 enabled on pin PIO0_6.
            value: 0
          - name: DISABLED
            description: ADC_1 disabled.
            value: 1
      - name: ADC_2
        description: ADC_2 function select.
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
        enumeratedValues:
          - name: ENABLED
            description: ADC_11 enabled on pin PIO0_4.
            value: 0
          - name: DISABLED
            description: ADC_11 disabled.
            value: 1
addressBlocks:
  - offset: 0
    size: 452
    usage: registers
