s13n/AES42HAT/fw/src/channel.cpp

/** @file
 * object representing a channel with one SRC4392
 * @addtogroup Channel
 * @ingroup AES42HAT
 * @{
 */
module;
#include <cstddef>
#include <cstdint>
#include "externs.h"
#include "coroutine.hpp"
module channel;


bool Channel::select(uint8_t tgt) {
    print("S");
    if ((tgt >> 1) != (0x70 + in_.in.addr))
        return false;
    expectReg_ = !(tgt & 0x01);
    return true;
}

void Channel::deselect() {
    print("D\n");
}

uint8_t Channel::getTxByte() {
    print("T");
    std::byte *ptr = src_.getPtr(addr_ & 0x7F, page_);
    if (bool inc = addr_ & 0x80)
        addr_ = (addr_ + 1) | 0x80;
    return ptr ? uint8_t(*ptr) : 0;
}

void Channel::putRxByte(uint8_t val) {
    print("R");
    if (expectReg_) {
        addr_ = val;
        expectReg_ = false;
        return;
    }
    std::byte *ptr = src_.getPtr(addr_ & 0x7F, page_);
    if (bool inc = addr_ & 0x80)
        addr_ = (addr_ + 1) | 0x80;
    if (ptr) {
        *ptr = std::byte(val);
        if (uint8_t(page_) == 0x00)
            pg0wb_ = true;
        if (uint8_t(page_) == 0x02)
            pg2wb_ = true;
    }
}

void Channel::isr() {
    uint16_t ts1 = ftm_.getCount();
    uint16_t capt = ftm_.getCapture(in_.tch);
    uint16_t ref = ftm_.getCapture(in_.rch);
    uint16_t ts2 = ftm_.getCount();
    delta_ = capt - ref;
    pint_.disable(in_.irq);
    pg1rd_ = true;
    post();
}

void Channel::act() {
    CORO_REENTER(coro_) {
        if (rstat_) {
            rstat_ = false;
            CORO_YIELD src_.readRxStatus(spiq_);
            print("S");
        } else if (pg1rd_) {
            pg1rd_ = false;
            CORO_YIELD src_.switchPage(spiq_, 0x01);
            CORO_YIELD src_.readCS(spiq_);
            CORO_YIELD src_.readU(spiq_);
            CORO_YIELD src_.switchPage(spiq_, 0x00);
            print("R");
        } else if (pg0wb_) {
            pg0wb_ = false;
            CORO_YIELD src_.writeRegs(spiq_);
            print("C");
        } else if (pg2wb_) {
            pg2wb_ = false;
            CORO_YIELD src_.readTxStatus(spiq_);
            CORO_YIELD src_.switchPage(spiq_, 0x02);
            CORO_YIELD src_.writeCS(spiq_);
            CORO_YIELD src_.writeU(spiq_);
            CORO_YIELD src_.switchPage(spiq_, 0x00);
            print("T");
        }
        pint_.enable(in_.irq, 4);
    }
}

Channel::Channel(Integration const &in, lpc865::SpiQueue &spiq, lpc865::Ftm &ftm, lpc865::Pint &pint)
    : addr_{0}
    , expectReg_{false}
    , page_{0}
    , pg0wb_{false}
    , pg2wb_{false}
    , rstat_{false}
    , pg1rd_{false}
    , in_{in}
    , spiq_{spiq}
    , ftm_{ftm}
    , pint_{pint}
    , src_{in.in, this}
{
    src_.updateRegs(in_.init);
    pint_.attach(in_.irq, 4, *this);
}
