s13n/AES42HAT/fw/src/wkt_drv.cpp

/** @file
 * driver for the LPC8 WKT
 * @addtogroup LPC865_wkt
 * @ingroup LPC865
 * @{
 */
module;
#include <cstdint>
module wkt_drv;
import WKT;

using namespace lpc865::WKT;

void lpc865::Wkt::isr() {
    auto &hw = *in_.registers;
    hw.CTRL.set(hw.CTRL.get());     // clear ALARMFLAG if set
    if (hdl_)
        hdl_->post();
}

void lpc865::Wkt::start(uint32_t count, Handler &hdl) {
    hdl_ = &hdl;
    in_.registers->COUNT.set(count);
}

lpc865::Wkt::Wkt(Intgr const &in, Parameters const &par)
    : in_{in}
    , hdl_{nullptr}
{
    auto &hw = *in_.registers;
    hw.CTRL = CTRL{ .CLKSEL = par.clksel, .ALARMFLAG = 1, .CLEARCTR = CLEAR_THE_COUNTER, .SEL_EXTCLK = par.extclk };

    insert(in_.exWKT);
}

/** @}*/
